gdellis/LoRaPaws32/resources/LoRaPaws32.jpg

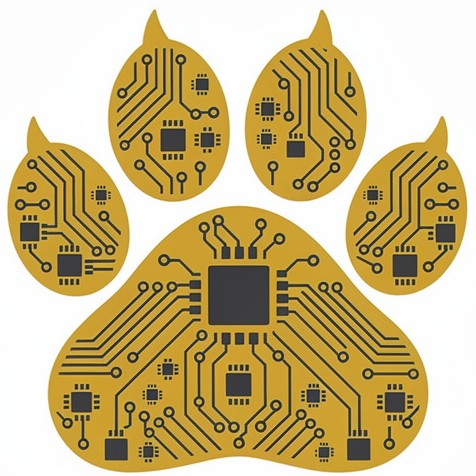
resources/LoRaPaws32.jpg
