gdellis/LoRaPaws32/firmware/main/geofence.cpp

#include "geofence.hpp"
#include <math.h>

#ifndef M_PI
#define M_PI 3.14159265358979323846
#endif

#define EARTH_RADIUS_METERS 6371000

static double
to_radians (int32_t degrees_e6) {
	return (static_cast<double> (degrees_e6) / 1000000.0) * (M_PI / 180.0);
}

bool
coordinates_valid (int32_t lat, int32_t lon) {
	constexpr int32_t MAX_LAT = 90 * 1000000;
	constexpr int32_t MIN_LAT = -90 * 1000000;
	constexpr int32_t MAX_LON = 180 * 1000000;
	constexpr int32_t MIN_LON = -180 * 1000000;

	return (lat >= MIN_LAT && lat <= MAX_LAT) && (lon >= MIN_LON && lon <= MAX_LON);
}

void
zone_set_name (CircleZone& zone, const char* name) {
	strncpy (zone.name, name, sizeof (zone.name) - 1);
	zone.name[sizeof (zone.name) - 1] = '\0';
}

int64_t
haversine_distance (int32_t lat1, int32_t lon1, int32_t lat2, int32_t lon2) {
	double lat1_rad = to_radians (lat1);
	double lat2_rad = to_radians (lat2);
	double dlat = to_radians (lat2 - lat1);
	double dlon = to_radians (lon2 - lon1);

	double a = sin (dlat / 2) * sin (dlat / 2)
			   + cos (lat1_rad) * cos (lat2_rad) * sin (dlon / 2) * sin (dlon / 2);

	double c = 2 * atan2 (sqrt (a), sqrt (1 - a));

	return (int64_t)(EARTH_RADIUS_METERS * c);
}

bool
point_in_circle (const GeoPoint& point, const CircleZone& zone) {
	if (!coordinates_valid (point.latitude, point.longitude)) {
		return false;
	}
	if (!coordinates_valid (zone.center.latitude, zone.center.longitude)) {
		return false;
	}

	int64_t distance = haversine_distance (point.latitude, point.longitude, zone.center.latitude,
										   zone.center.longitude);
	return distance <= zone.radius_m;
}

bool
polygon_add_vertex (PolygonZone& zone, int32_t lat, int32_t lon) {
	if (zone.vertex_count >= 16) {
		return false;
	}
	zone.vertices[zone.vertex_count].latitude = lat;
	zone.vertices[zone.vertex_count].longitude = lon;
	zone.vertex_count++;
	return true;
}

bool
point_in_polygon (const GeoPoint& point, const PolygonZone& zone) {
	if (!coordinates_valid (point.latitude, point.longitude)) {
		return false;
	}
	if (zone.vertex_count < 3) {
		return false;
	}

	bool inside = false;
	double x = static_cast<double> (point.longitude) / COORD_SCALE;
	double y = static_cast<double> (point.latitude) / COORD_SCALE;

	for (uint8_t i = 0, j = zone.vertex_count - 1; i < zone.vertex_count; j = i++) {
		double xi = static_cast<double> (zone.vertices[i].longitude) / COORD_SCALE;
		double yi = static_cast<double> (zone.vertices[i].latitude) / COORD_SCALE;
		double xj = static_cast<double> (zone.vertices[j].longitude) / COORD_SCALE;
		double yj = static_cast<double> (zone.vertices[j].latitude) / COORD_SCALE;

		if (((yi > y) != (yj > y)) && (x < (xj - xi) * (y - yi) / (yj - yi) + xi)) {
			inside = !inside;
		}
	}

	return inside;
}
