gdellis/LoRaPaws32/build.rs

fn main() {
    linker_be_nice();
    println!("cargo:rustc-link-arg=-Tlinkall.x");
}

fn linker_be_nice() {
    let args: Vec<String> = std::env::args().collect();
    if args.len() > 1 {
        let kind = &args[1];
        let what = &args[2];

        match kind.as_str() {
            "undefined-symbol" => match what.as_str() {
                what if what.starts_with("_defmt_") => {
                    eprintln!();
                    eprintln!("defmt not found - make sure defmt.x is added as a linker script");
                    eprintln!();
                }
                "_stack_start" => {
                    eprintln!();
                    eprintln!("Is the linker script linkall.x missing?");
                    eprintln!();
                }
                what if what.starts_with("esp_rtos_") => {
                    eprintln!();
                    eprintln!("esp-radio has no scheduler enabled");
                    eprintln!();
                }
                _ => (),
            },
            _ => {
                std::process::exit(1);
            }
        }

        std::process::exit(0);
    }

    println!(
        "cargo:rustc-link-arg=-Wl,--error-handling-script={}",
        std::env::current_exe().unwrap().display()
    );
}
