gdellis/LoRaPaws32/firmware/tests/include/esp_log.h

#ifndef TEST_MOCKS_ESP_LOG_H
#define TEST_MOCKS_ESP_LOG_H

#define ESP_LOGD(tag, format, ...) do {} while(0)
#define ESP_LOGI(tag, format, ...) do {} while(0)
#define ESP_LOGW(tag, format, ...) do {} while(0)
#define ESP_LOGE(tag, format, ...) do {} while(0)

#endif
